collaborative-music-lab/ESP_MIDI/Enclosure/Knobs/knurledKnobFlatWide_20mmTop-pointB-Circle_001.stl

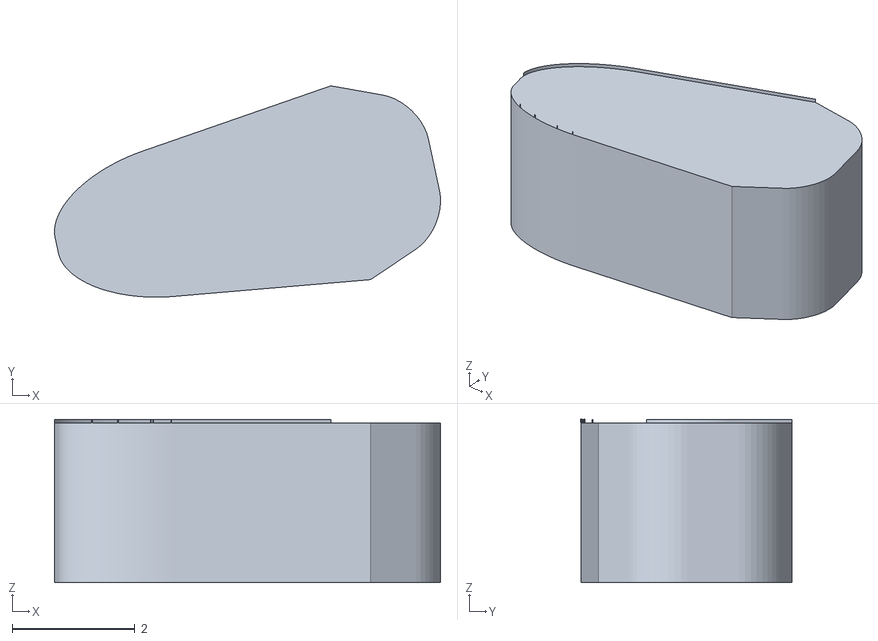
[picture p11: CAD file, 2024-07-09]
Enclosure/Knobs/knurledKnobFlatWide_20mmTop-pointB-Circle_001.stl
6.29 x 3.45 x 2.66
