collaborative-music-lab/ESP_MIDI/Enclosure/MIDI_PCB.stl

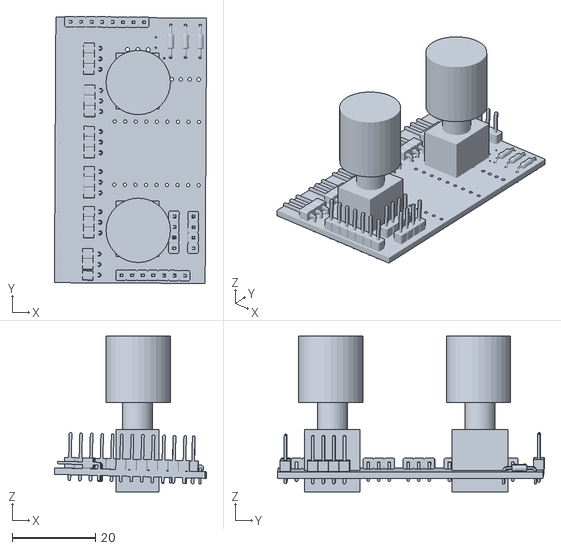
[picture p12: CAD file, 2024-07-09]
Enclosure/MIDI_PCB.stl
36.7 x 64.3 x 37.5
