collaborative-music-lab/ESP_MIDI/PCB/Kicad/Main-PCB/Sum25_GTR/Enclosure/Two Straight Left Rack V3.stl

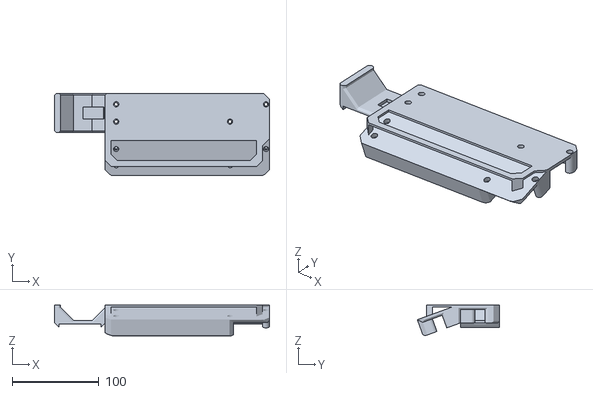
[picture p13: CAD file, 2025-08-03]
PCB/Kicad/Main-PCB/Sum25_GTR/Enclosure/Two Straight Left Rack V3.stl
248.2 x 95.1 x 35.3
