collaborative-music-lab/ESP_MIDI/PCB/Kicad/Main-PCB/Sum25_Wand_v2/ESP32_MIDI_WAND.step

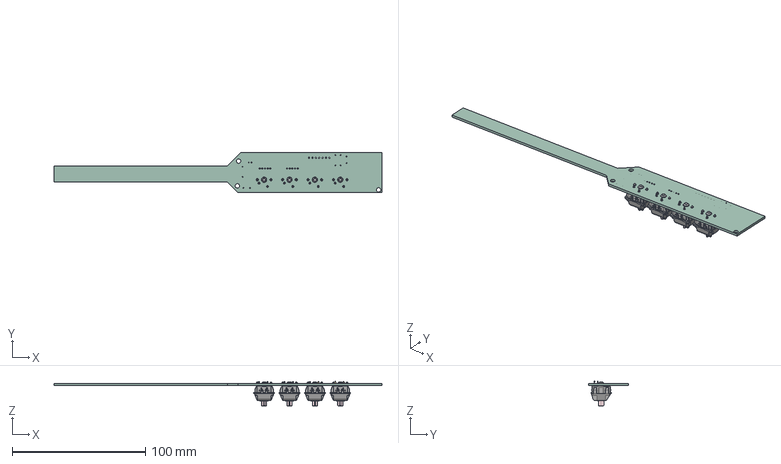
[picture p14: CAD file, 2025-06-30]
PCB/Kicad/Main-PCB/Sum25_Wand_v2/ESP32_MIDI_WAND.step
246.0 x 30.0 x 18.4 mm
silent_alpaca x 4
ESP32_MIDI_Summer25_Wand_PCB
