collaborative-music-lab/ESP_MIDI/Enclosure/1590BB.stl

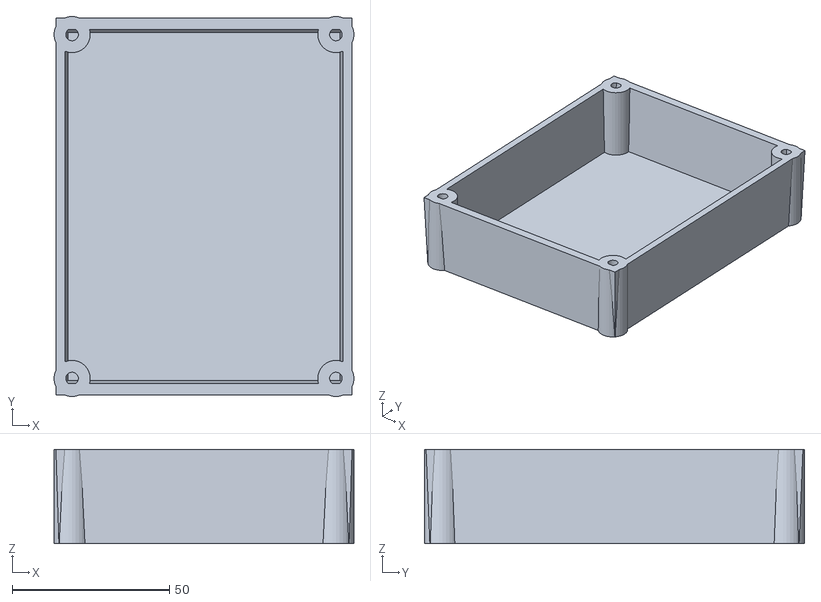
[picture p15: CAD file, 2024-07-09]
Enclosure/1590BB.stl
95.5 x 121.0 x 30.0
