collaborative-music-lab/ESP_MIDI/Enclosure/Faceplates/1590BB_cover3-Top_002.stl

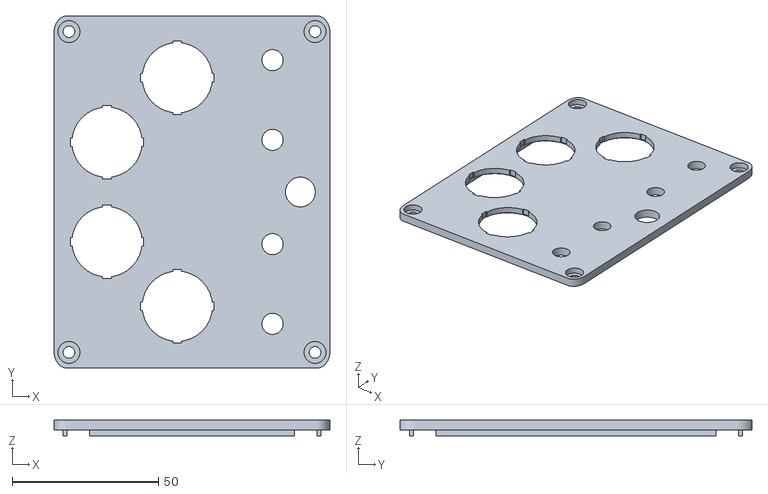
[picture p16: CAD file, 2024-07-15]
Enclosure/Faceplates/1590BB_cover3-Top_002.stl
94.2 x 120.2 x 5.38
