collaborative-music-lab/ESP_MIDI/PCB/Kicad/Main-PCB/mbira/mbriaPCB_v0_3-SHAPE_385_IndexedFaceSet.stl

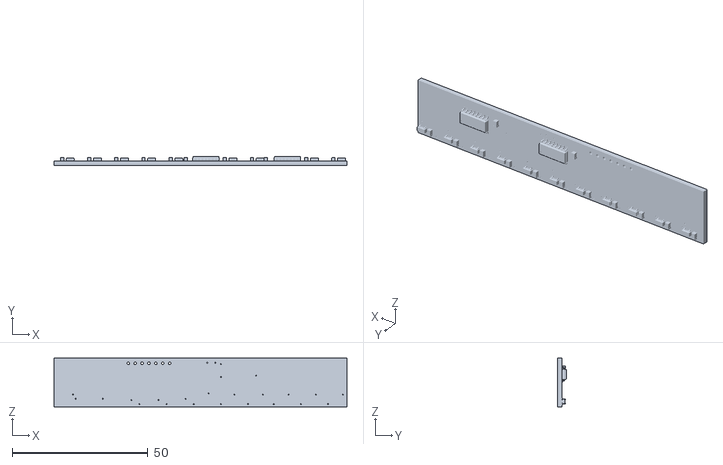
[picture p17: CAD file, 2026-02-26]
PCB/Kicad/Main-PCB/mbira/mbriaPCB_v0_3-SHAPE_385_IndexedFaceSet.stl
108.0 x 3.43 x 18.0
