collaborative-music-lab/ESP_MIDI/PCB/Kicad/Main-PCB/Sum25_GTR/Enclosure/Hooks V5 (1).stl

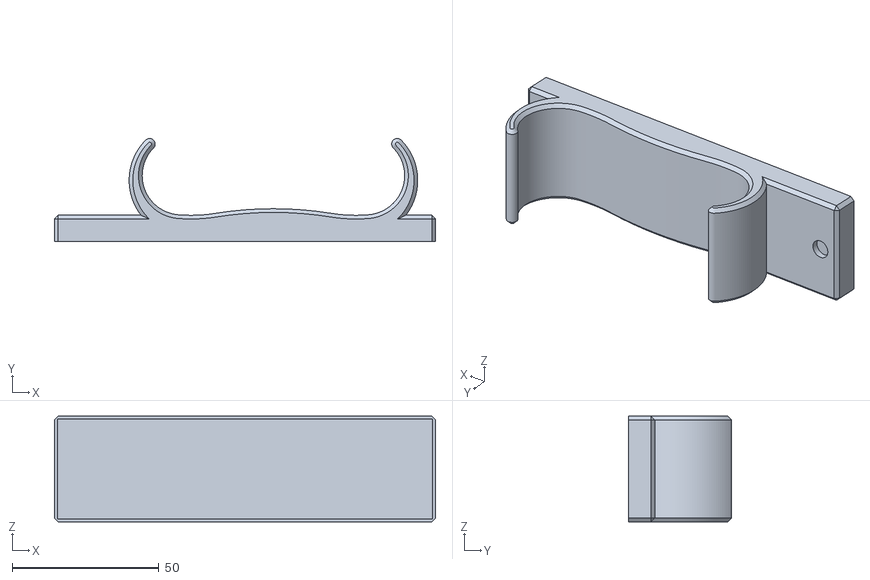
[picture p18: CAD file, 2025-08-03]
PCB/Kicad/Main-PCB/Sum25_GTR/Enclosure/Hooks V5 (1).stl
130.0 x 35.2 x 36.0
