collaborative-music-lab/ESP_MIDI/Enclosure/arcade_button_29mm.stl

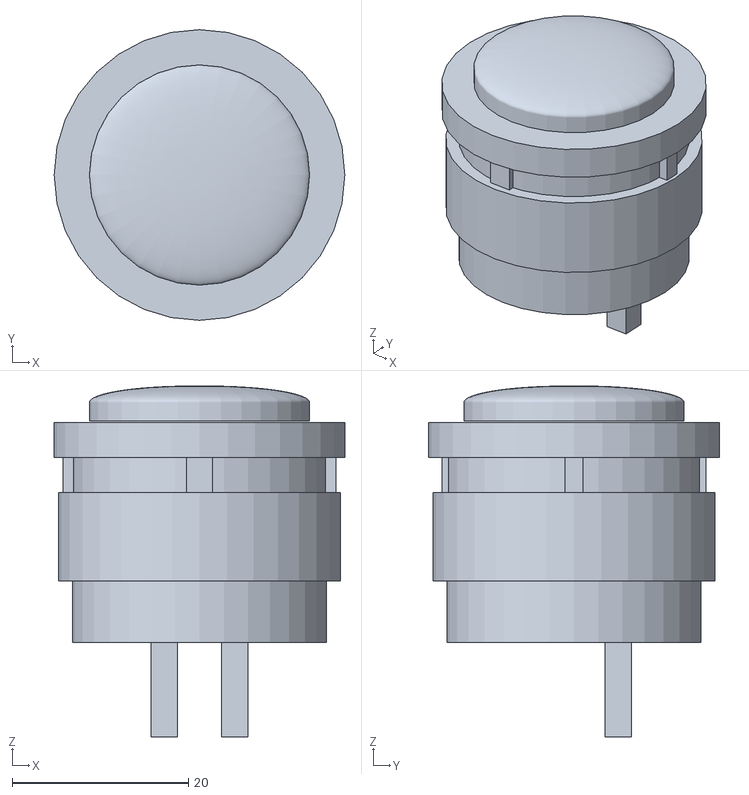
[picture p19: CAD file, 2024-07-09]
Enclosure/arcade_button_29mm.stl
33.0 x 33.0 x 39.8
