collaborative-music-lab/ESP_MIDI/PCB/Kicad/Main-PCB/Sum25_GTR/Enclosure/Fret Stands.stl

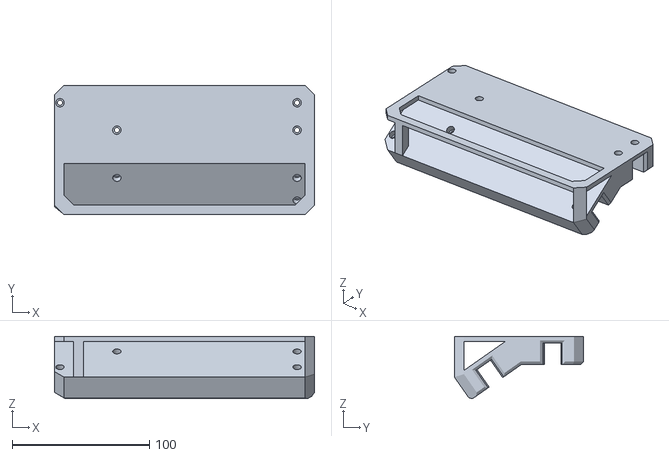
[picture p20: CAD file, 2025-08-03]
PCB/Kicad/Main-PCB/Sum25_GTR/Enclosure/Fret Stands.stl
189.7 x 94.3 x 45.4
