collaborative-music-lab/ESP_MIDI/Enclosure/pot_RK07.stl

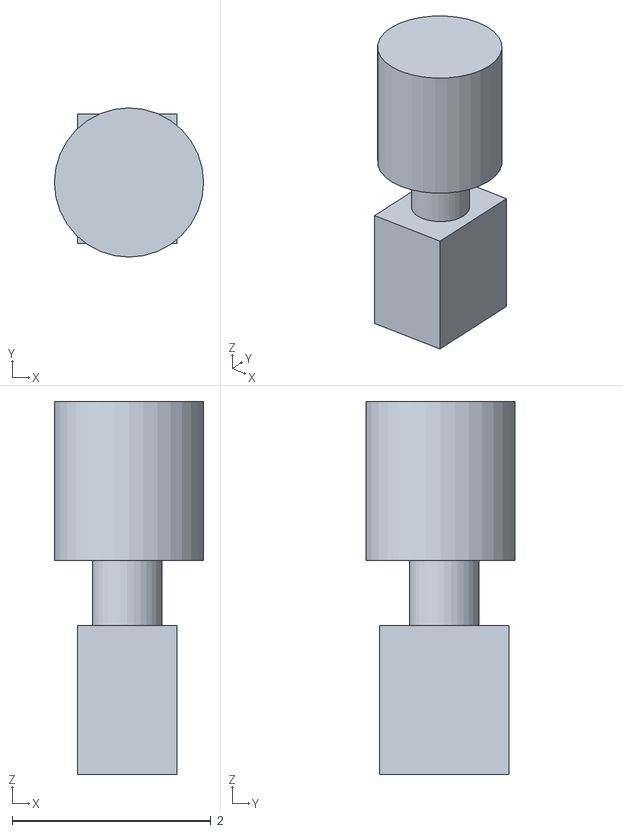
[picture p21: CAD file, 2024-07-09]
Enclosure/pot_RK07.stl
1.50 x 1.50 x 3.75
