collaborative-music-lab/ESP_MIDI/Enclosure/arcade_button_23mm.stl

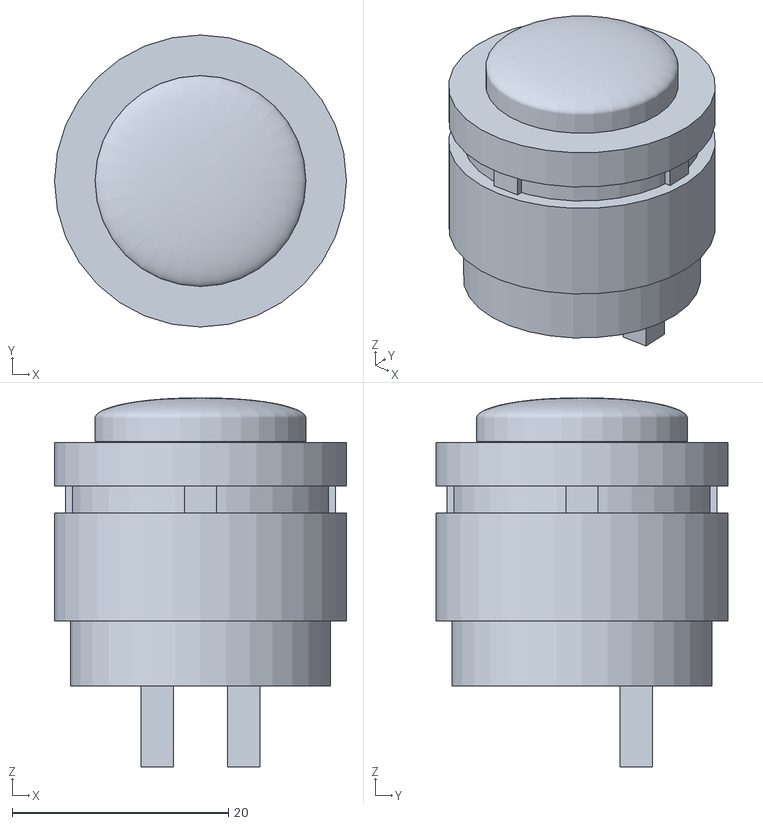
[picture p22: CAD file, 2024-07-09]
Enclosure/arcade_button_23mm.stl
27.0 x 27.0 x 34.1
