collaborative-music-lab/ESP_MIDI/PCB/Kicad/Main-PCB/Sum25_GTR/Enclosure/Varied Fret Left Rack V3.stl

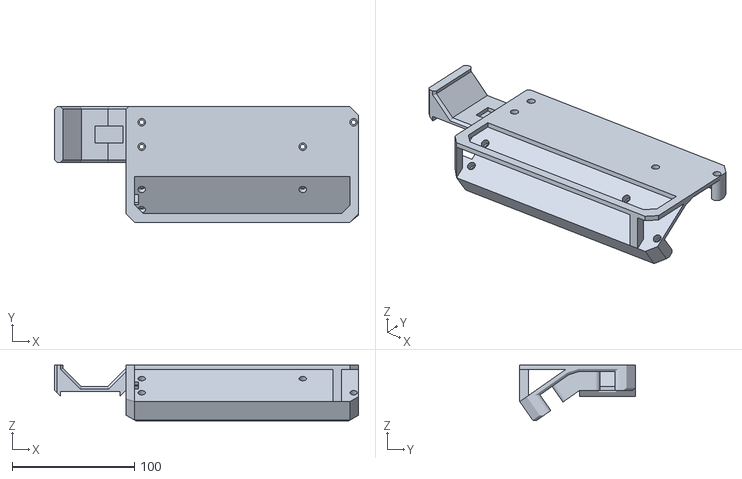
[picture p23: CAD file, 2025-08-03]
PCB/Kicad/Main-PCB/Sum25_GTR/Enclosure/Varied Fret Left Rack V3.stl
248.2 x 94.3 x 45.4
