collaborative-music-lab/ESP_MIDI/PCB/Kicad/Main-PCB/Sum25_GTR/Enclosure/Triple Brace V1.stl

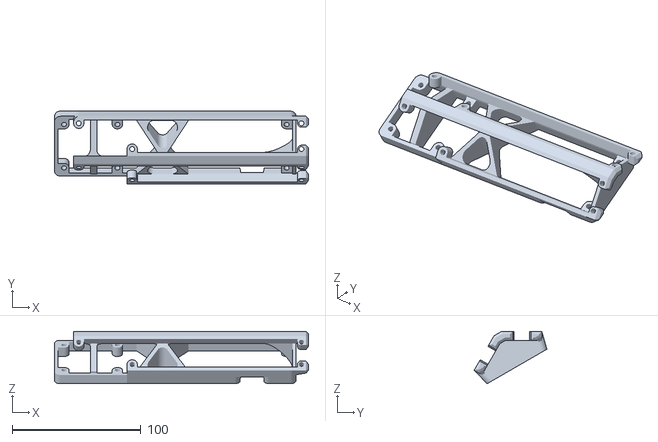
[picture p24: CAD file, 2025-08-03]
PCB/Kicad/Main-PCB/Sum25_GTR/Enclosure/Triple Brace V1.stl
197.3 x 56.6 x 40.8
