collaborative-music-lab/ESP_MIDI/PCB/Kicad/Main-PCB/Sum25_GTR/Enclosure/Two Straight Left Rack.stl

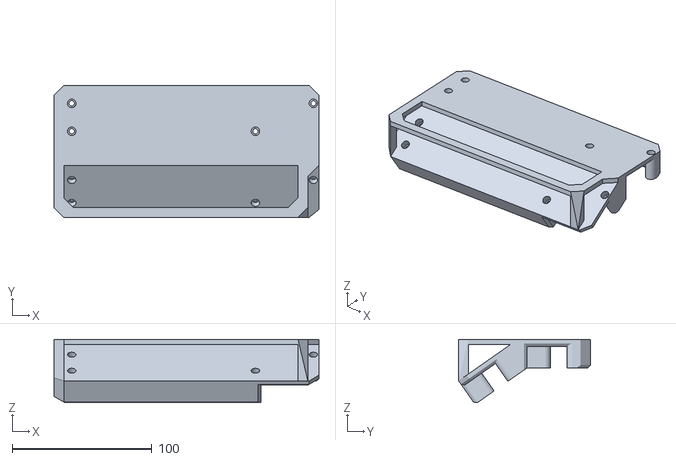
[picture p25: CAD file, 2025-08-03]
PCB/Kicad/Main-PCB/Sum25_GTR/Enclosure/Two Straight Left Rack.stl
189.7 x 94.3 x 45.4
