collaborative-music-lab/ESP_MIDI/PCB/Kicad/Main-PCB/Sum25_GTR/Enclosure/One Bar Hook.stl

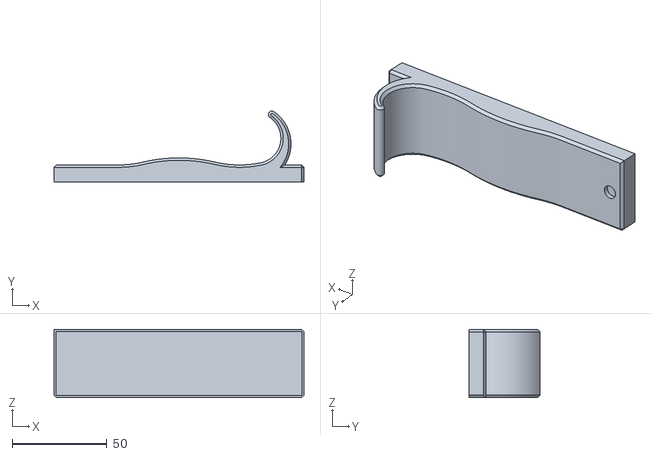
[picture p26: CAD file, 2025-08-03]
PCB/Kicad/Main-PCB/Sum25_GTR/Enclosure/One Bar Hook.stl
132.0 x 37.4 x 36.0
