collaborative-music-lab/ESP_MIDI/PCB/Kicad/Main-PCB/Robin_v2_2/Robin_v2_2.kicad_pcb

## KiCad design PCB/Kicad/Main-PCB/Robin_v2_2/Robin_v2_2.kicad_pcb (2025-07-27)

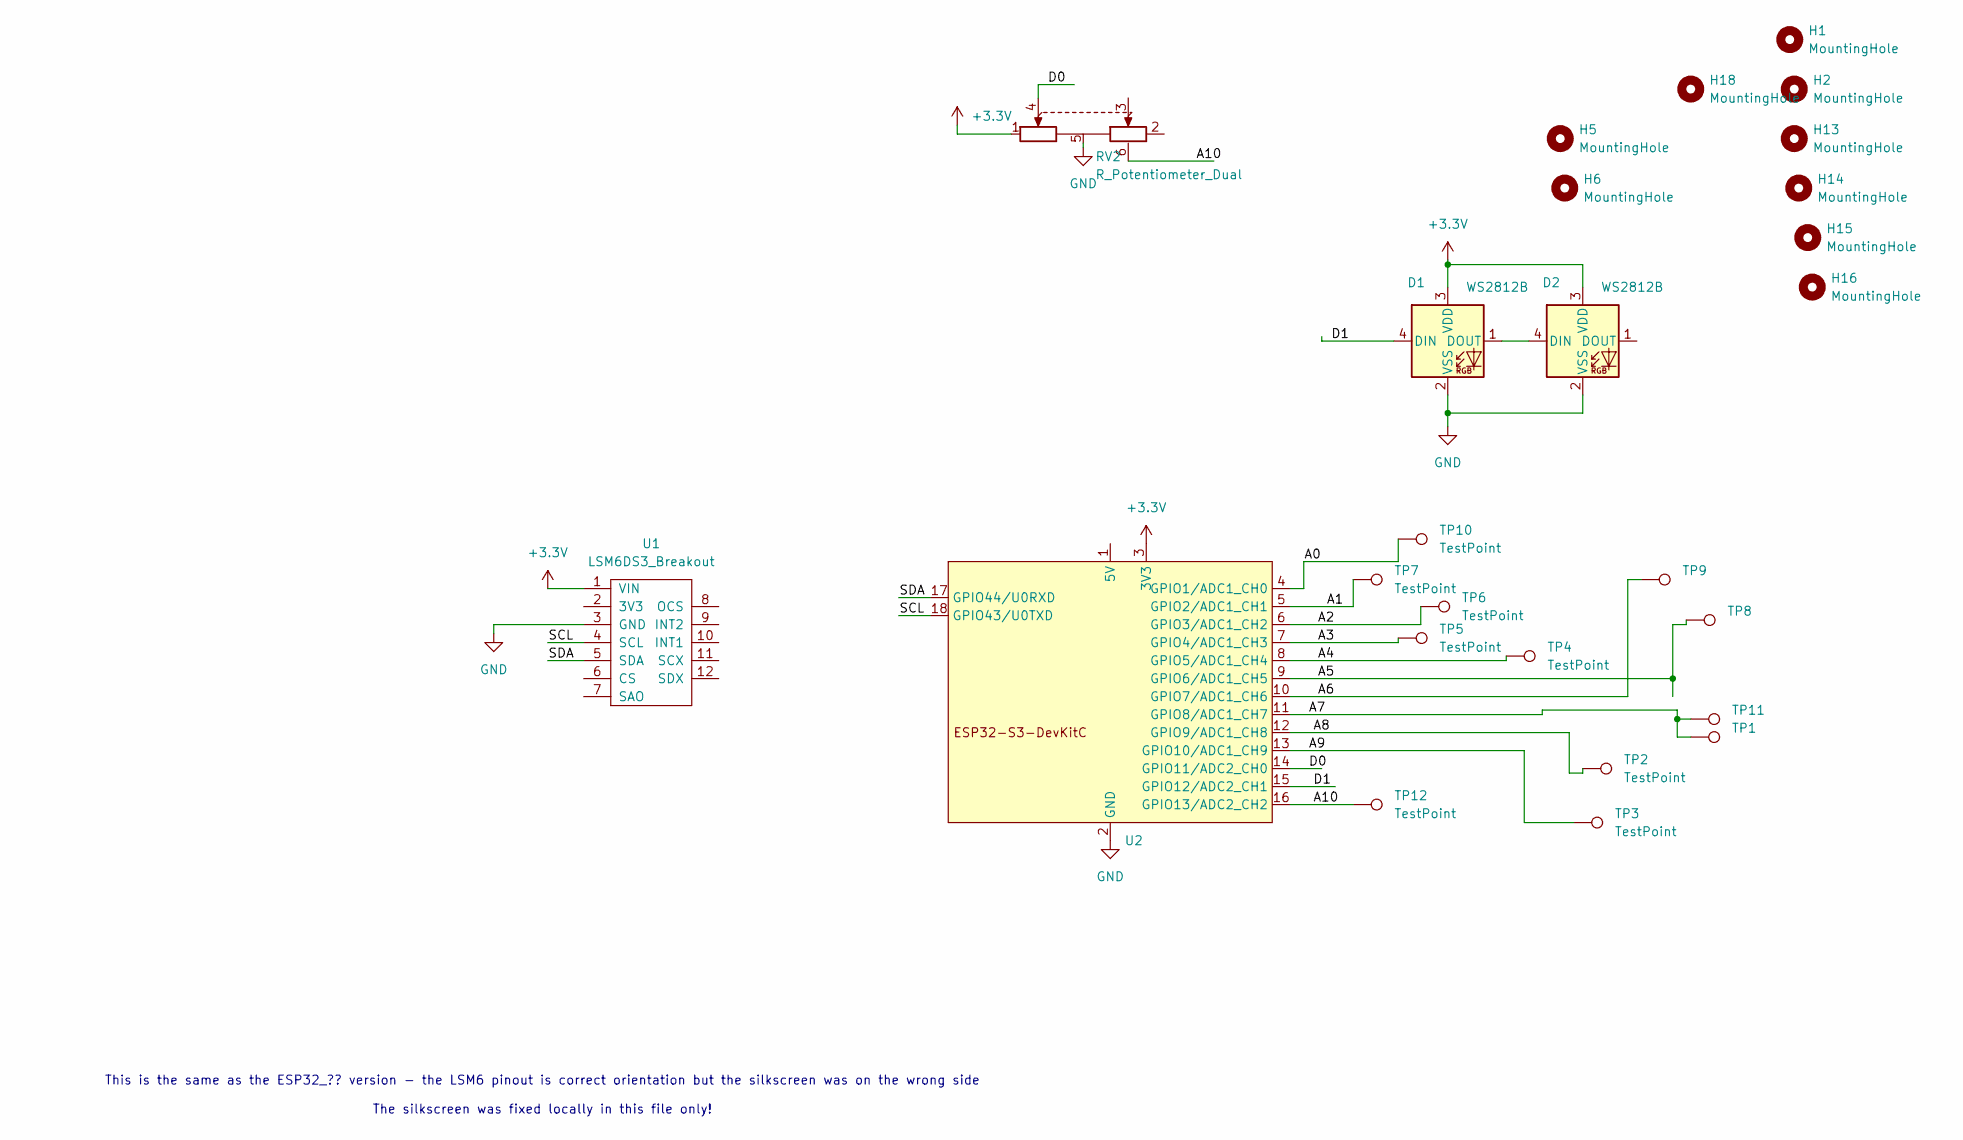
[picture p51: schematic Robin_v2_2.kicad_sch]

Parts:
D1, D2: WS2812B; LED_D5.0mm-4_RGB_Wide_Pins
H1, H2, H13, H14, H15, H16, H18: MountingHole; MountingHole_4.5mm
H5, H6: MountingHole; MountingHole_3.2mm_M3_ISO14580
RV2: R_Potentiometer_Dual; potentiometer_wheel_10mm_SMD-shield
TP1, TP2, TP3, TP4, TP5, TP6, TP7, TP10: TestPoint; recorder-touchpad
TP8, TP12: TestPoint; recorder-touchpad-alt-up
TP9: TestPoint; recorder-touchtrack_120mm
TP11: TestPoint; recorder-touchpad-narrow
U1: LSM6DS3_Breakout; LSM6DS3_Breakout_oneSide
U2: Wifiduino-ESP32S3-SMD

Connections:
+3.3V: D1.3 (VDD), D2.3 (VDD), RV2.1 (1A), U1.1 (VIN), U2.3 (3V3)
/A0: TP10.1, U2.4 (GPIO1/ADC1_CH0)
/A1: TP7.1, U2.5 (GPIO2/ADC1_CH1)
/A2: TP6.1, U2.6 (GPIO3/ADC1_CH2)
/A3: TP5.1, U2.7 (GPIO4/ADC1_CH3)
/A4: TP4.1, U2.8 (GPIO5/ADC1_CH4)
/A5: TP8.1, U2.9 (GPIO6/ADC1_CH5)
/A6: TP9.1, U2.10 (GPIO7/ADC1_CH6)
/A7: TP1.1, TP11.1, U2.11 (GPIO8/ADC1_CH7)
/A8: TP2.1, U2.12 (GPIO9/ADC1_CH8)
/A9: TP3.1, U2.13 (GPIO10/ADC1_CH9)
/A10: RV2.6 (Shield), TP12.1, U2.16 (GPIO13/ADC2_CH2)
/D0: RV2.4 (1-Wiper), U2.14 (GPIO11/ADC2_CH0)
/D1: D1.4 (DIN), U2.15 (GPIO12/ADC2_CH1)
/SCL: U1.4 (SCL), U2.18 (GPIO43/U0TXD)
/SDA: U1.5 (SDA), U2.17 (GPIO44/U0RXD)
GND: D1.2 (VSS), D2.2 (VSS), RV2.5 (Common), U1.3 (GND), U2.2 (GND)
unnamed: D1.1 (DOUT), D2.4 (DIN)

Notes on the sheet:
This is the same as the ESP32_?? version - the LSM6 pinout is correct orientation but the silkscreen was on the wrong side The silkscreen was fixed locally in this file only!

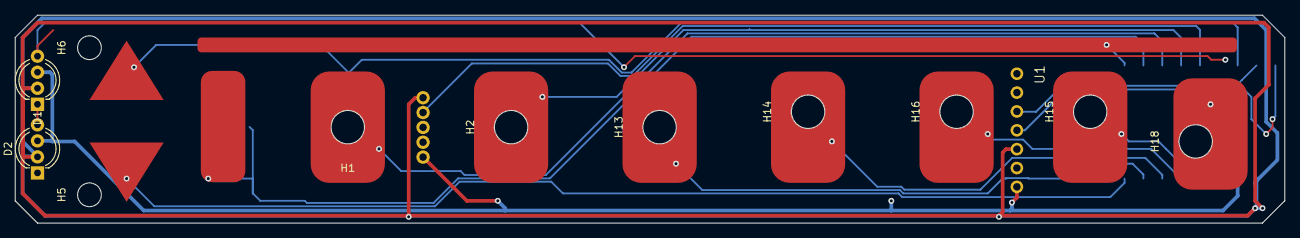
[picture p52: board Robin_v2_2.kicad_pcb from above]

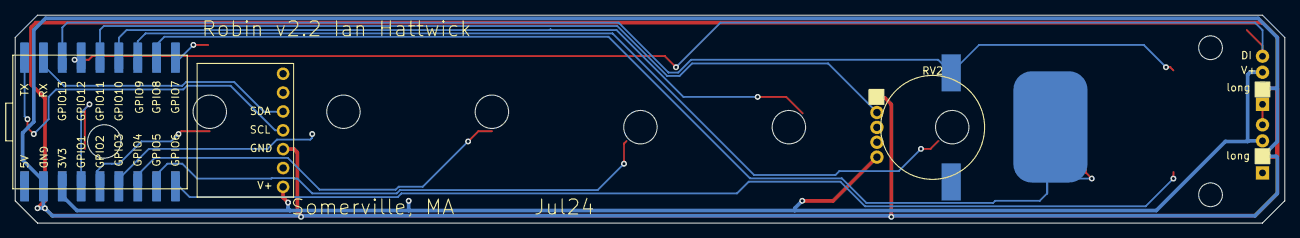
[picture p53: board Robin_v2_2.kicad_pcb from below]

Board: 2 copper layers, 171.0 x 28.0 mm, 26 parts (3 on the bottom side), 18 nets.
