collaborative-music-lab/ESP_MIDI/PCB/Kicad/Main-PCB/ESP32_MIDI_Summer25_FRETS_v2_5.kicad_pcb/ESP32_MIDI_Summer25_FRETS_v2_5.kicad_pcb.kicad_pcb

## KiCad design PCB/Kicad/Main-PCB/ESP32_MIDI_Summer25_FRETS_v2_5.kicad_pcb/ESP32_MIDI_Summer25_FRETS_v2_5.kicad_pcb.kicad_pcb (2025-07-27)

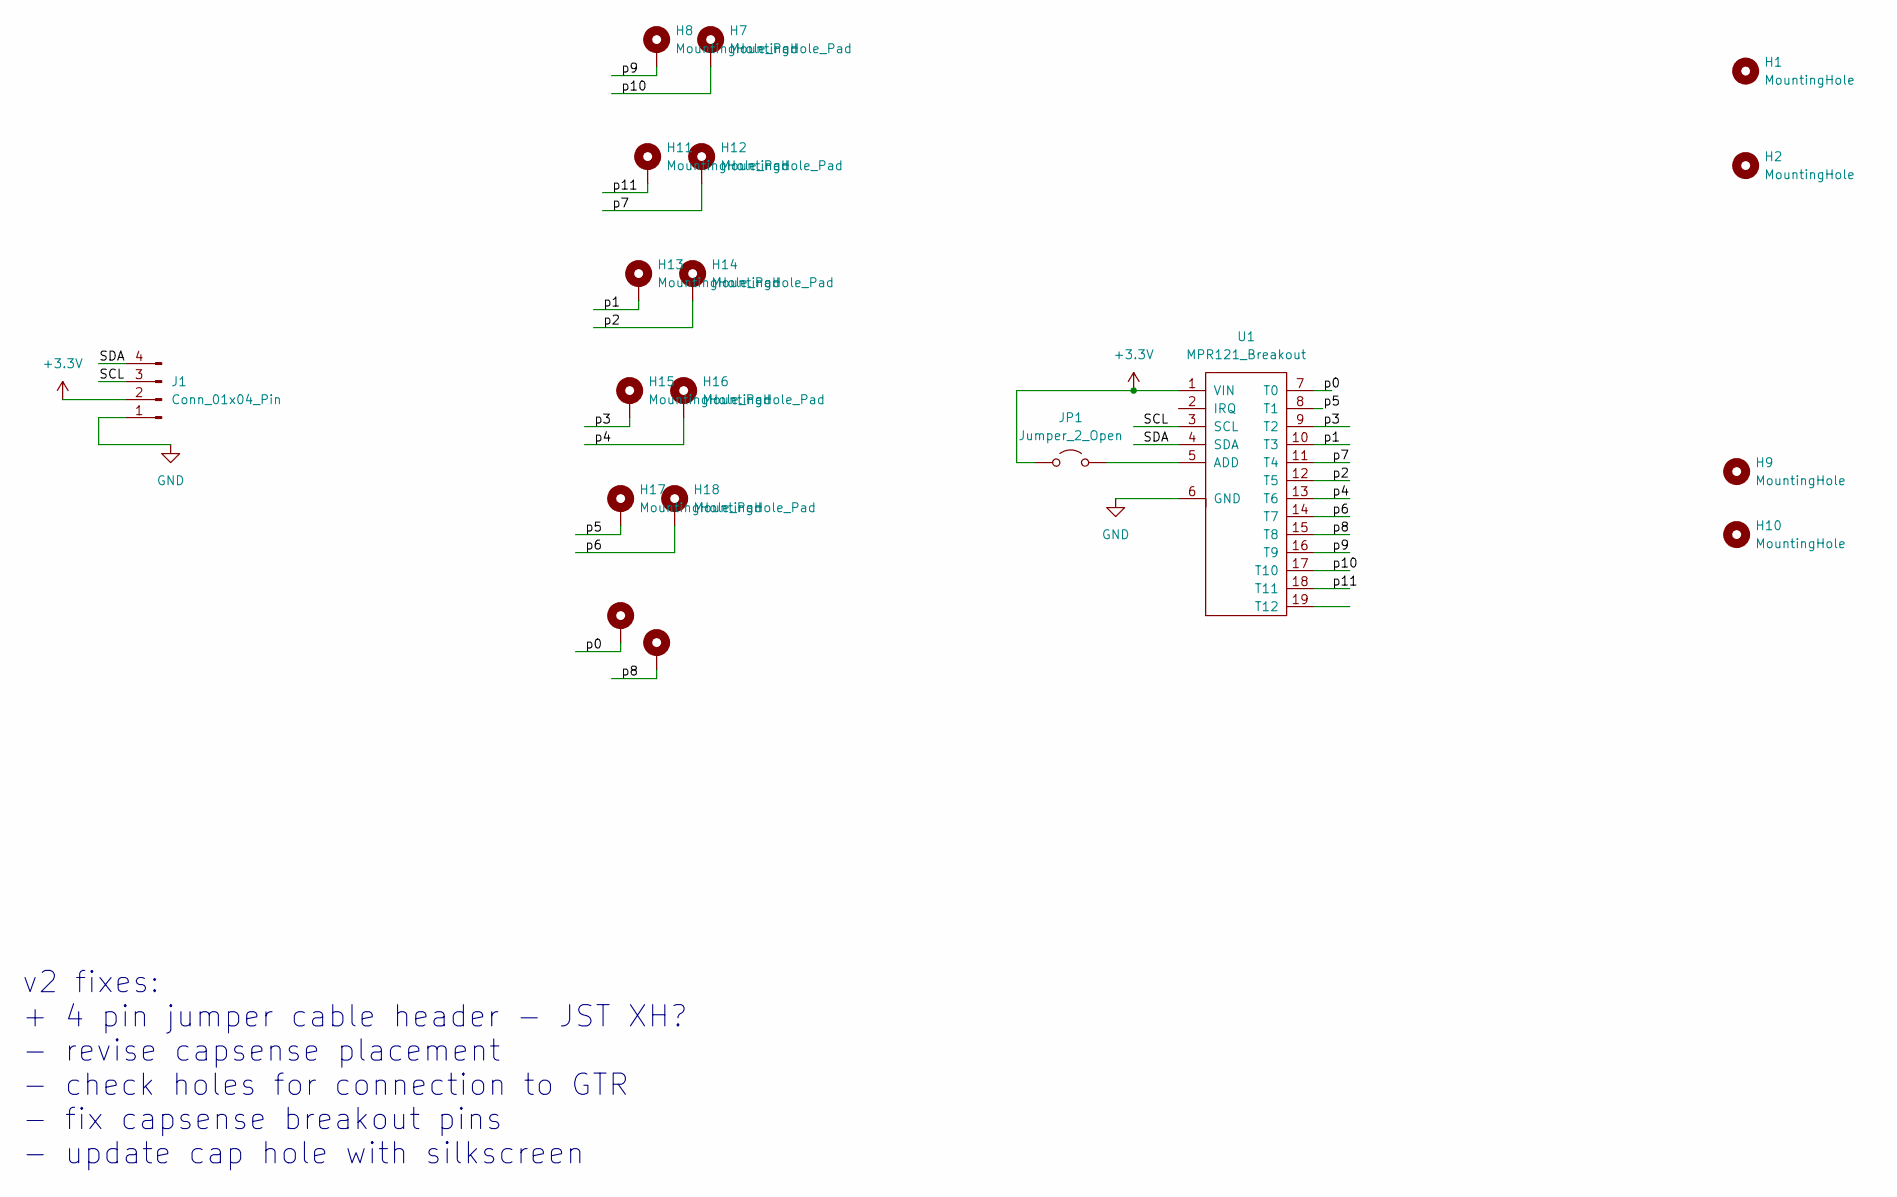
[picture p54: schematic ESP32_MIDI_Summer25_FRETS_v2_5.kicad_pcb.kicad_sch]

Parts:
H1, H2: MountingHole; MountingHole_4.3mm_M4
H3, H7, H8, H11, H12, H13, H14, H15, H16, H17, H18, H19: MountingHole_Pad; MountingHole_6.4mm_M6_DIN965_Pad_TopBottom
H9, H10: MountingHole; MountingHole_3.2mm_M3
J1: Conn_01x04_Pin; PinHeader_1x04_P2.54mm_Horizontal
JP1: Jumper_2_Open; SolderJumper-2_P1.3mm_Open_RoundedPad1.0x1.5mm
U1: MPR121_Breakout

Connections:
+3.3V: J1.2, JP1.1 (A), U1.1 (VIN)
/SCL: J1.3, U1.3 (SCL)
/SDA: J1.4, U1.4 (SDA)
/p0: H19.1, U1.7 (T0)
/p1: H13.1, U1.10 (T3)
/p2: H14.1, U1.12 (T5)
/p3: H15.1, U1.9 (T2)
/p4: H16.1, U1.13 (T6)
/p5: H17.1, U1.8 (T1)
/p6: H18.1, U1.14 (T7)
/p7: H12.1, U1.11 (T4)
/p8: H3.1, U1.15 (T8)
/p9: H8.1, U1.16 (T9)
/p10: H7.1, U1.17 (T10)
/p11: H11.1, U1.18 (T11)
GND: J1.1, U1.6 (GND)
unnamed: JP1.2 (B), U1.5 (ADD)

Notes on the sheet:
v2 fixes: + 4 pin jumper cable header - JST XH? - revise capsense placement - check holes for connection to GTR - fix capsense breakout pins - update cap hole with silkscreen

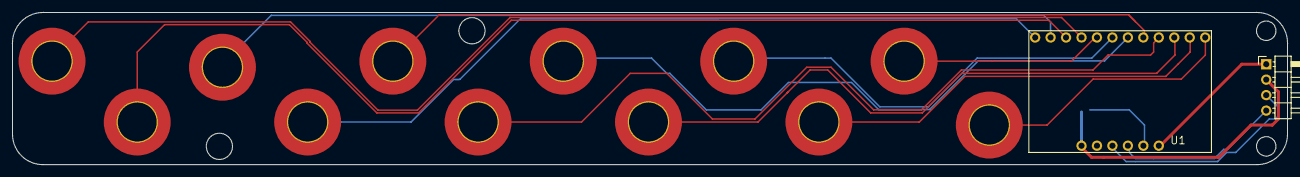
[picture p55: board ESP32_MIDI_Summer25_FRETS_v2_5.kicad_pcb.kicad_pcb from above]

Board: 2 copper layers, 209.5 x 25.0 mm, 19 parts (1 on the bottom side), 17 nets.
