collaborative-music-lab/ESP_MIDI/PCB/Kicad/Main-PCB/Sum25_GTR/Sum25_GTR.kicad_pcb

## KiCad design PCB/Kicad/Main-PCB/Sum25_GTR/Sum25_GTR.kicad_pcb (2025-07-27)

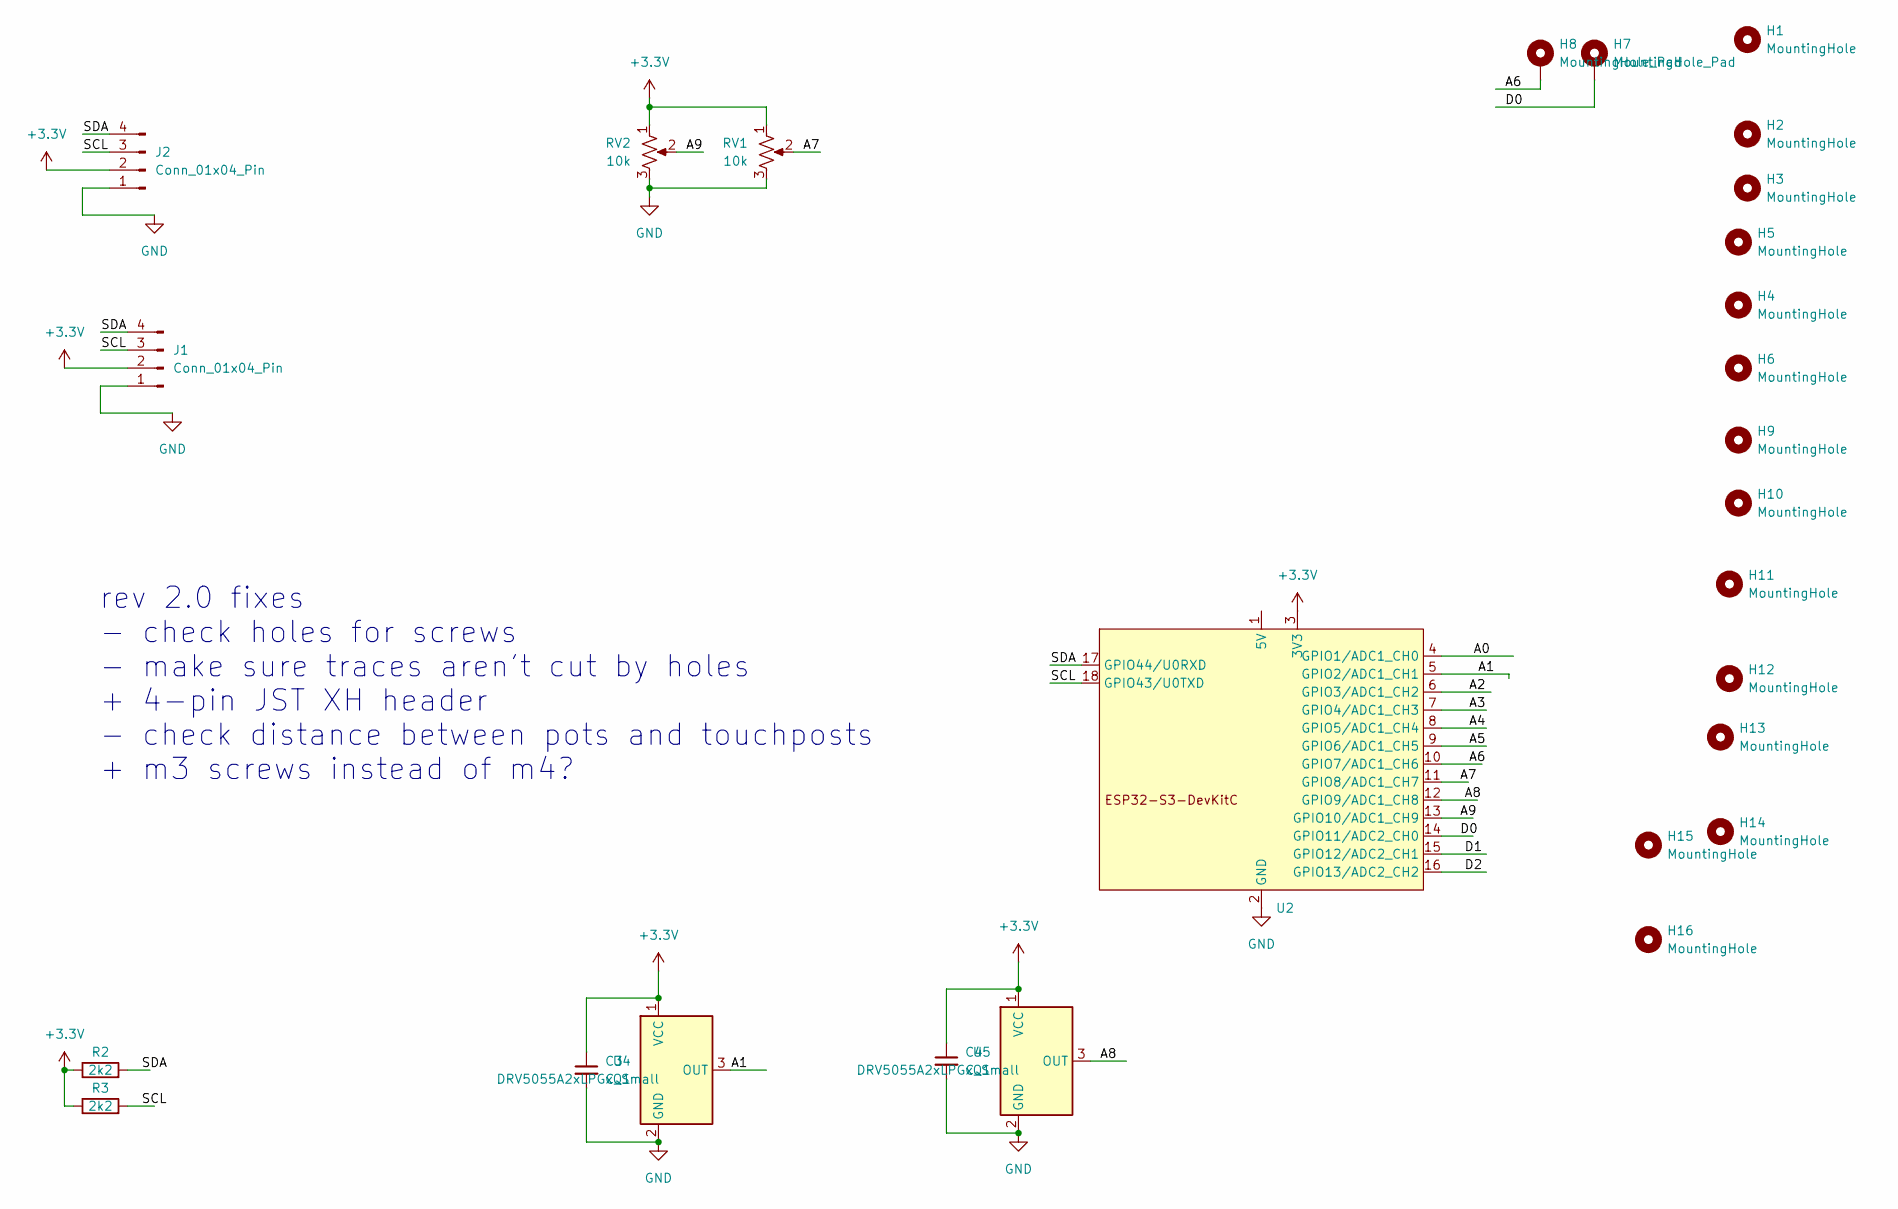
[picture p56: schematic Sum25_GTR.kicad_sch]

Parts:
C3, C4: C_Small; C_Disc_D6.0mm_W2.5mm_P5.00mm
H1, H2, H3, H4, H5, H6, H9, H10, H11, H12, H13, H14, H15, H16: MountingHole; MountingHole_3.2mm_M3
H7, H8: MountingHole_Pad; MountingHole_6.4mm_M6_DIN965_Pad_TopBottom
J1, J2: Conn_01x04_Pin; PinSocket_1x04_P2.54mm_Vertical
R2, R3: 2k2; R_Axial_DIN0204_L3.6mm_D1.6mm_P7.62mm_Horizontal
RV1, RV2: 10k; Potentiometer_Alps_RK09K_Single_Vertical
U2: Wifiduino-ESP32S3-SMD
U4, U5: DRV5055A2xLPGxQ1; TO-92_flat

Connections:
+3.3V: C3.1, C4.1, J1.2, J2.2, R2.1, R3.1, RV1.1, RV2.1, U2.3 (3V3), U4.1 (VCC), U5.1 (VCC)
/A0: U2.4 (GPIO1/ADC1_CH0)
/A1: U2.5 (GPIO2/ADC1_CH1), U4.3 (OUT)
/A2: U2.6 (GPIO3/ADC1_CH2)
/A3: U2.7 (GPIO4/ADC1_CH3)
/A4: U2.8 (GPIO5/ADC1_CH4)
/A5: U2.9 (GPIO6/ADC1_CH5)
/A6: H8.1, U2.10 (GPIO7/ADC1_CH6)
/A7: RV1.2, U2.11 (GPIO8/ADC1_CH7)
/A8: U2.12 (GPIO9/ADC1_CH8), U5.3 (OUT)
/A9: RV2.2, U2.13 (GPIO10/ADC1_CH9)
/D0: H7.1, U2.14 (GPIO11/ADC2_CH0)
/D1: U2.15 (GPIO12/ADC2_CH1)
/D2: U2.16 (GPIO13/ADC2_CH2)
/SCL: J1.3, J2.3, R3.2, U2.18 (GPIO43/U0TXD)
/SDA: J1.4, J2.4, R2.2, U2.17 (GPIO44/U0RXD)
GND: C3.2, C4.2, J1.1, J2.1, RV1.3, RV2.3, U2.2 (GND), U4.2 (GND), U5.2 (GND)

Notes on the sheet:
rev 2.0 fixes - check holes for screws - make sure traces aren't cut by holes + 4-pin JST XH header - check distance between pots and touchposts + m3 screws instead of m4?

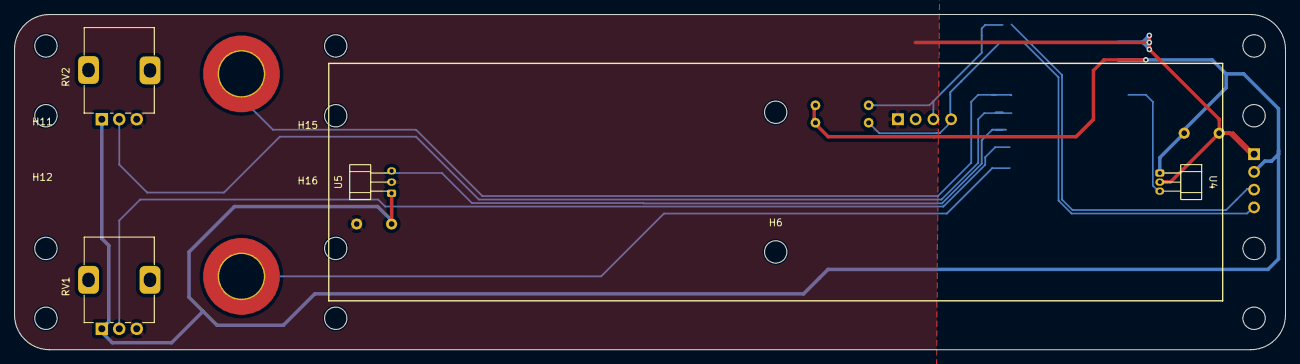
[picture p57: board Sum25_GTR.kicad_pcb from above]

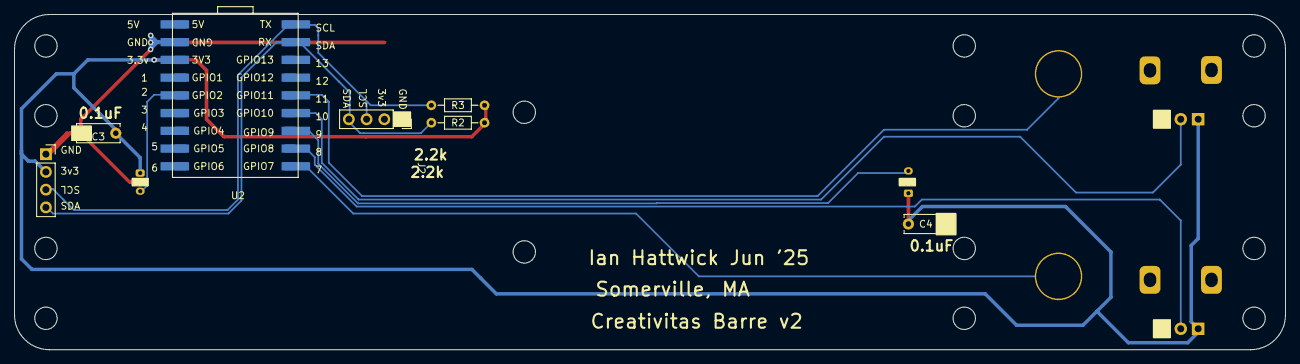
[picture p58: board Sum25_GTR.kicad_pcb from below]

Board: 2 copper layers, 182.0 x 48.0 mm, 27 parts (7 on the bottom side), 10 nets.
