collaborative-music-lab/ESP_MIDI/PCB/Kicad/Main-PCB/Sum25_Wand_v2/Sum25_Wand_v2.kicad_pcb

## KiCad design PCB/Kicad/Main-PCB/Sum25_Wand_v2/Sum25_Wand_v2.kicad_pcb (2025-07-03)

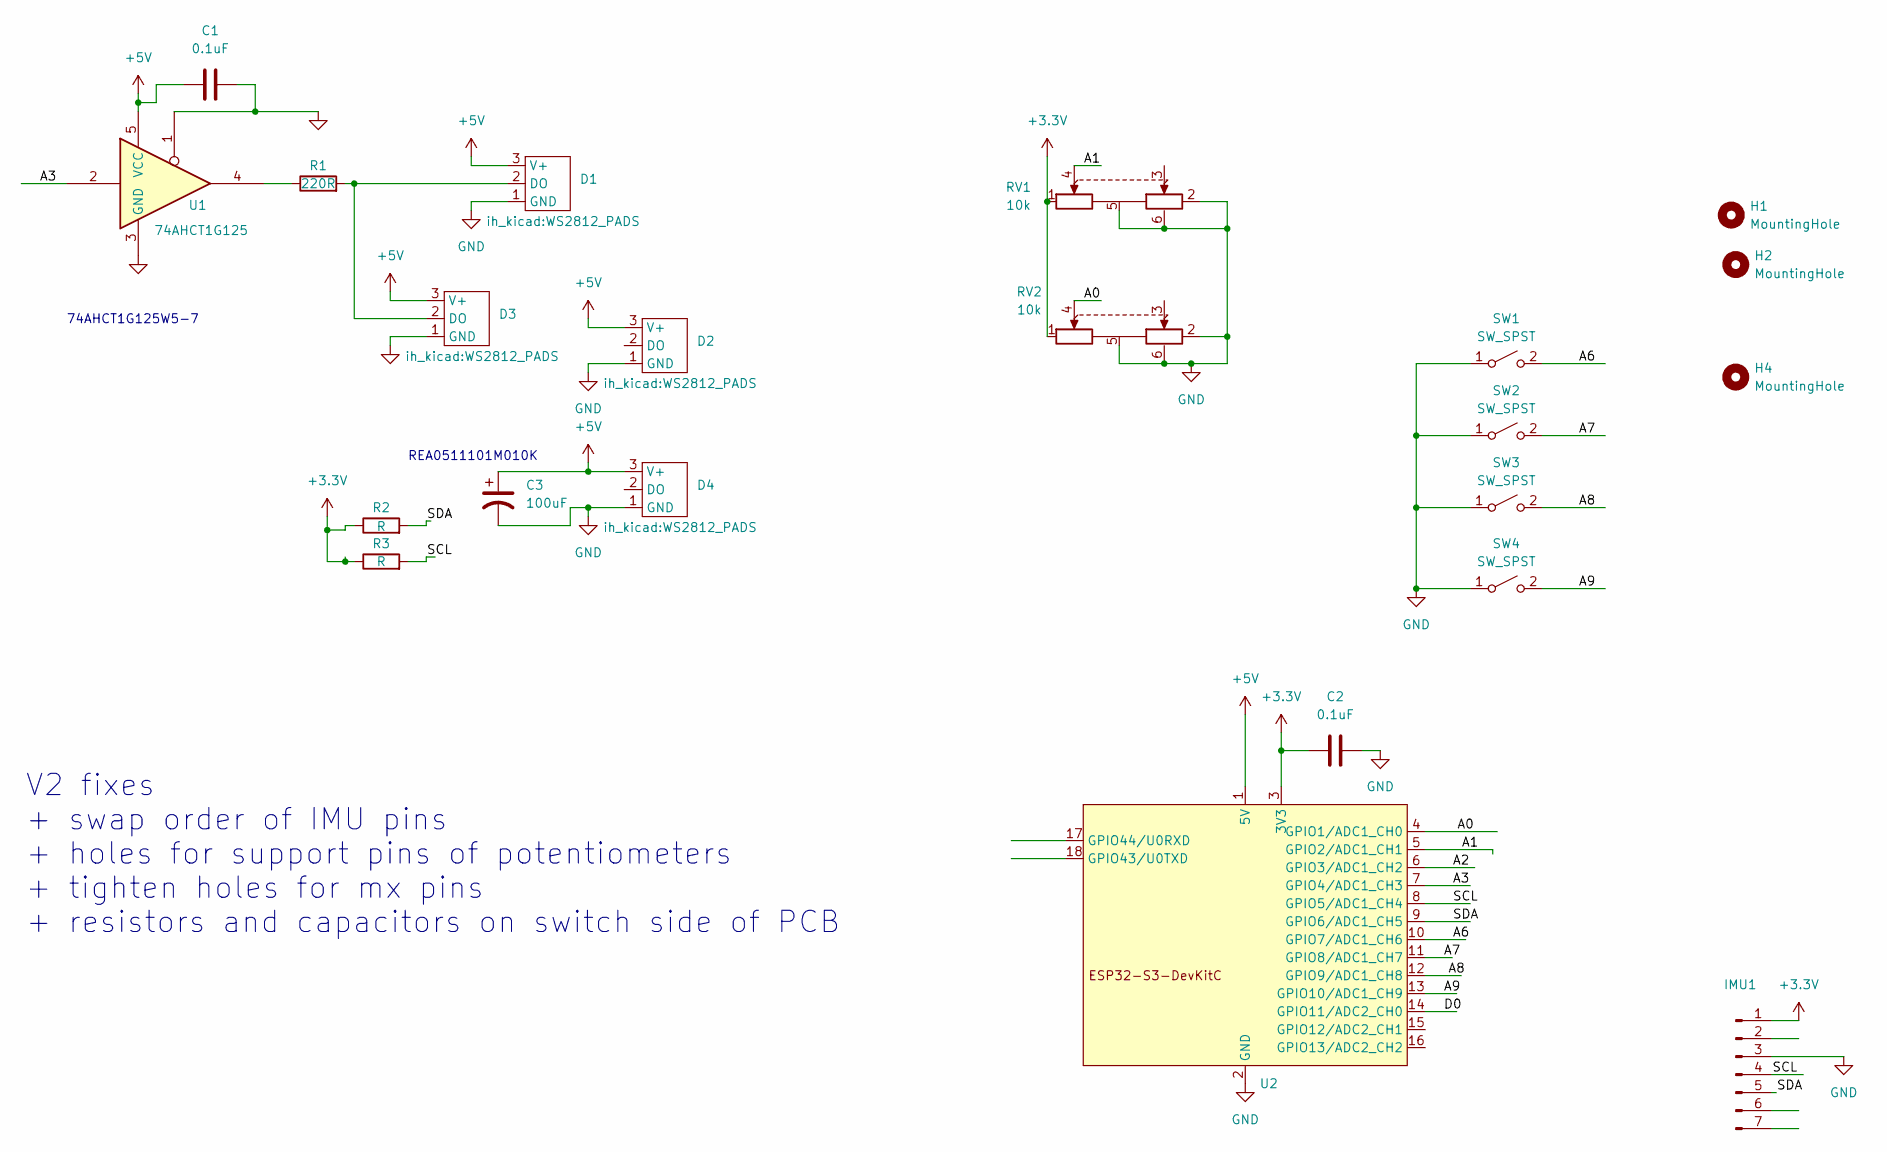
[picture p59: schematic Sum25_Wand_v2.kicad_sch]

Parts:
C1, C2: 0.1uF; C_Disc_D5.1mm_W3.2mm_P5.00mm
C3: 100uF; CP_Radial_D5.0mm_P2.00mm
D1, D2, D3, D4: WS2812_PADS
H1, H2, H4: MountingHole; MountingHole_3.2mm_M3
IMU1: Conn_01x07_Pin; PinHeader_1x07_P2.54mm_Vertical
R1: 220R; R_Axial_DIN0204_L3.6mm_D1.6mm_P7.62mm_Horizontal
R2, R3: R; R_Axial_DIN0204_L3.6mm_D1.6mm_P7.62mm_Horizontal
RV1, RV2: 10k; potentiometer_wheel_10mm
SW1, SW2, SW3, SW4: SW_SPST; SW_Cherry_MX_1.00u_Plate
U1: 74AHCT1G125; TSOT-23-5_HandSoldering
U2: Wifiduino-ESP32S3-SMD

Connections:
+3.3V: C2.2, IMU1.1, R2.1, R3.1, RV1.1 (1A), RV2.1 (1A), U2.3 (3V3)
+5V: C1.1, C3.1, D1.3 (V+), D2.3 (V+), D3.3 (V+), D4.3 (V+), U1.5 (VCC), U2.1 (5V)
/A0: RV2.4 (1-Wiper), U2.4 (GPIO1/ADC1_CH0)
/A1: RV1.4 (1-Wiper), U2.5 (GPIO2/ADC1_CH1)
/A2: U2.6 (GPIO3/ADC1_CH2)
/A3: U1.2, U2.7 (GPIO4/ADC1_CH3)
/A6: SW1.2 (B), U2.10 (GPIO7/ADC1_CH6)
/A7: SW2.2 (B), U2.11 (GPIO8/ADC1_CH7)
/A8: SW3.2 (B), U2.12 (GPIO9/ADC1_CH8)
/A9: SW4.2 (B), U2.13 (GPIO10/ADC1_CH9)
/D0: U2.14 (GPIO11/ADC2_CH0)
/SCL: IMU1.4, R3.2, U2.8 (GPIO5/ADC1_CH4)
/SDA: IMU1.5, R2.2, U2.9 (GPIO6/ADC1_CH5)
GND: C1.2, C2.1, C3.2, D1.1 (GND), D2.1 (GND), D3.1 (GND), D4.1 (GND), IMU1.3, RV1.2 (2B), RV1.5 (Common), RV1.6 (Shield), RV2.2 (2B), RV2.5 (Common), RV2.6 (Shield), SW1.1 (A), SW2.1 (A), SW3.1 (A), SW4.1 (A), U1.1, U1.3 (GND), U2.2 (GND)
unnamed: D1.2 (DO), D3.2 (DO), R1.2
unnamed: R1.1, U1.4

Notes on the sheet:
V2 fixes + swap order of IMU pins + holes for support pins of potentiometers + tighten holes for mx pins + resistors and capacitors on switch side of PCB
REA0511101M010K
74AHCT1G125W5-7

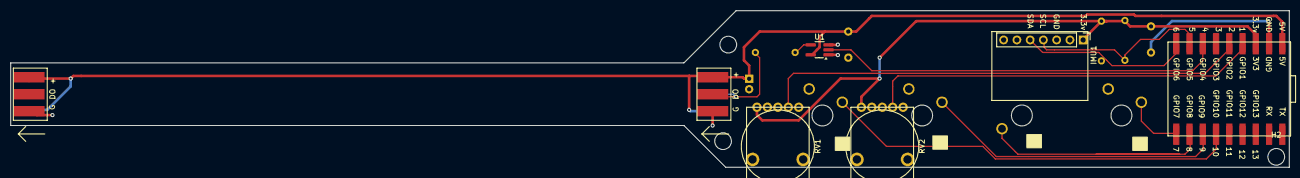
[picture p60: board Sum25_Wand_v2.kicad_pcb from above]

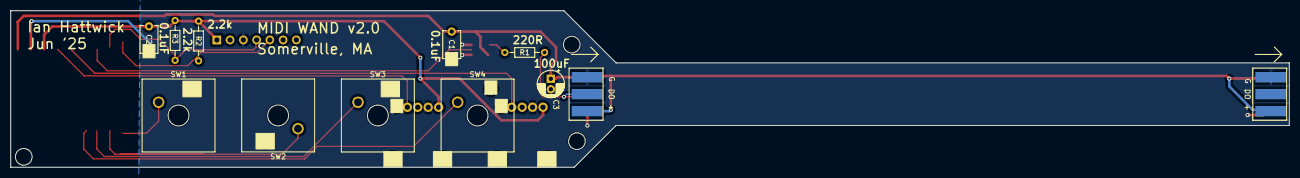
[picture p61: board Sum25_Wand_v2.kicad_pcb from below]

Board: 2 copper layers, 245.0 x 30.0 mm, 22 parts (12 on the bottom side), 14 nets.
