collaborative-music-lab/ESP_MIDI/PCB/Kicad/Main-PCB/ESP32_MIDI_v4/ESP32_MIDI_v4.kicad_pro/ESP32_MIDI_v4.kicad_pro.kicad_sch

## KiCad design PCB/Kicad/Main-PCB/ESP32_MIDI_v4/ESP32_MIDI_v4.kicad_pro/ESP32_MIDI_v4.kicad_pro.kicad_sch (2025-06-22)

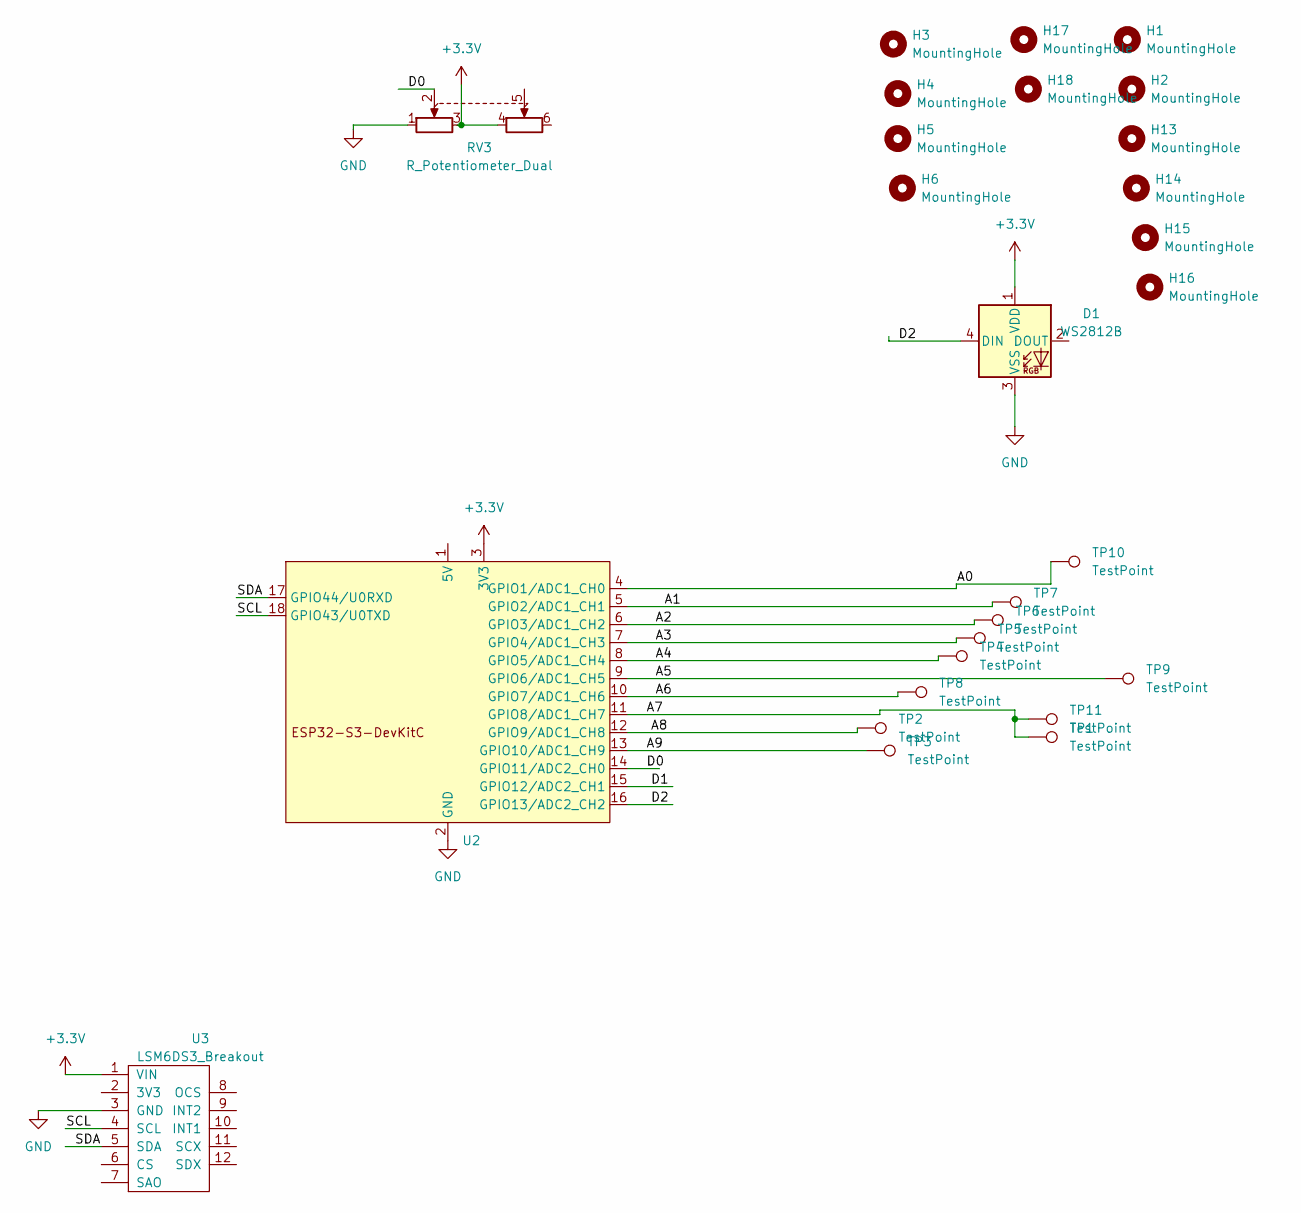
[picture p62: schematic ESP32_MIDI_v4.kicad_pro.kicad_sch]

Parts:
D1: WS2812B; LED_WS2812B_PLCC4_5.0x5.0mm_P3.2mm
H1, H2, H3, H4, H5, H6, H13, H14, H15, H16, H17, H18: MountingHole; MountingHole_3.2mm_M3
RV3: R_Potentiometer_Dual; potentiometer_wheel_16mm
TP1, TP2, TP3, TP4, TP5, TP6, TP7, TP10: TestPoint; recorder-touchpad
TP8, TP9: TestPoint; recorder-touchtrack
TP11: TestPoint; recorder-touchpad-narrow
U2: Wifiduino-ESP32S3-SMD
U3: LSM6DS3_Breakout; LSM6DS3_Breakout_oneSide

Connections:
+3.3V: D1.1 (VDD), RV3.3, RV3.4, U2.3 (3V3), U3.1 (VIN)
A0: TP10.1, U2.4 (GPIO1/ADC1_CH0)
A1: TP7.1, U2.5 (GPIO2/ADC1_CH1)
A2: TP6.1, U2.6 (GPIO3/ADC1_CH2)
A3: TP5.1, U2.7 (GPIO4/ADC1_CH3)
A4: TP4.1, U2.8 (GPIO5/ADC1_CH4)
A5: TP9.1, U2.9 (GPIO6/ADC1_CH5)
A6: TP8.1, U2.10 (GPIO7/ADC1_CH6)
A7: TP1.1, TP11.1, U2.11 (GPIO8/ADC1_CH7)
A8: TP2.1, U2.12 (GPIO9/ADC1_CH8)
A9: TP3.1, U2.13 (GPIO10/ADC1_CH9)
D0: RV3.2, U2.14 (GPIO11/ADC2_CH0)
D1: U2.15 (GPIO12/ADC2_CH1)
D2: D1.4 (DIN), U2.16 (GPIO13/ADC2_CH2)
GND: D1.3 (VSS), RV3.1, U2.2 (GND), U3.3 (GND)
SCL: U2.18 (GPIO43/U0TXD), U3.4 (SCL)
SDA: U2.17 (GPIO44/U0RXD), U3.5 (SDA)
