collaborative-music-lab/ESP_MIDI/instruments/mbira/imu_processing.py

import math
import time

def get_magnitude(data):
    """Calculates total force (Resultant Vector)"""
    mag = math.sqrt(sum(val**2 for val in data))
    return abs(mag-1)

def get_tilt_angles(accel):
    """
    Converts gravity distribution into Tilt (Degrees).
    Works best when the device is moving slowly.
    """
    x, y, z = accel
    # math.atan2 is safer than atan as it handles division by zero
    pitch = math.atan2(x, math.sqrt(y*y + z*z)) * 180 / math.pi
    roll = math.atan2(y, math.sqrt(x*x + z*z)) * 180 / math.pi
    yaw = math.atan2(z, math.sqrt(x*x + y*y)) * 180 / math.pi
    return pitch, roll, yaw

def get_gyro_angle(gyro_x, current_angle):
    """
    Integrates angular velocity to find position.
    Requires knowing how much time has passed (dt).
    """
    now = time.monotonic()
    dt = now - self.last_time
    self.last_time = now
    
    # New Angle = Old Angle + (Speed * Time)
    return current_angle + (gyro_x * dt)

def low_pass_filter(new_val, prev_filtered, alpha=0.1):
    """
    Smooths out jitter. 
    alpha 0.1 = 90% old data, 10% new data.
    """
    return (1 - alpha) * new_val + alpha * prev_filtered
def onepole(new_val, prev_filtered, alpha=0.1):
    return low_pass_filter(new_val, prev_filtered, alpha)

def smooth(new_val, prev_val, up=0.1, down=0.9):
    alpha = up
    if new_val < prev_val:
        alpha = down
    return low_pass_filter(new_val, prev_val, alpha)
